MukeshSankhla/Forest-Guard/images/3.png

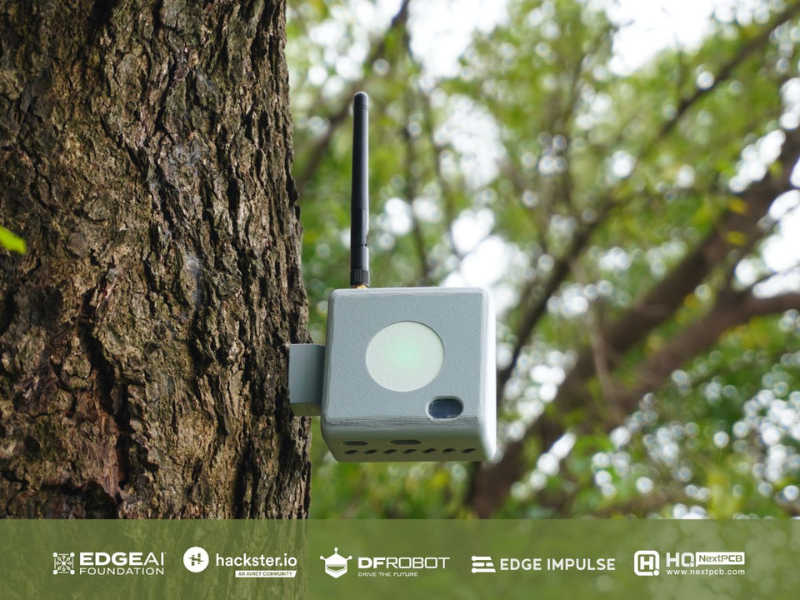
images/3.png
