MukeshSankhla/Forest-Guard/images/S91.JPG

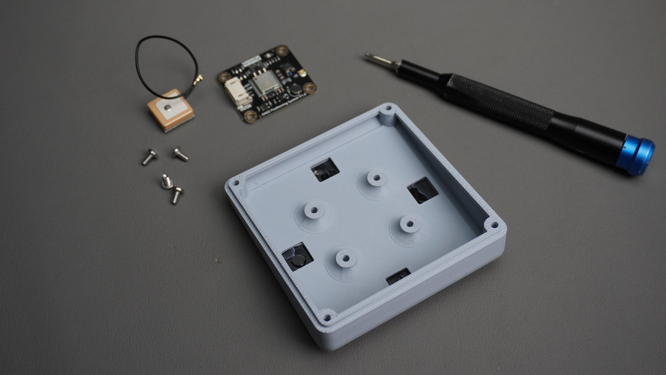
images/S91.JPG
