MukeshSankhla/Forest-Guard/images/ST268.JPG

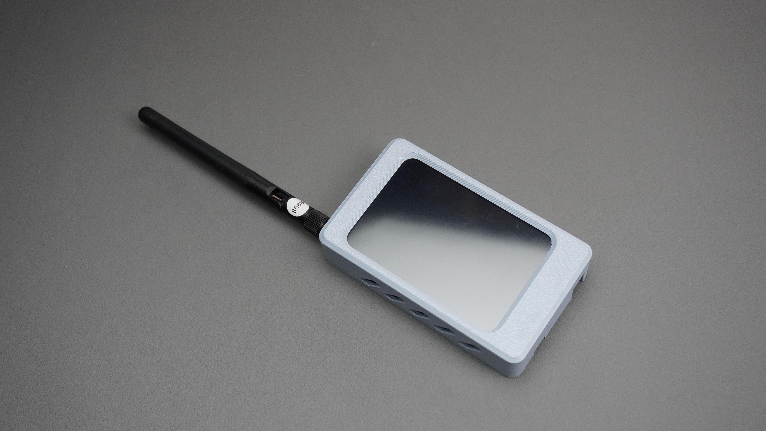
images/ST268.JPG
