MukeshSankhla/Forest-Guard/images/ST277.JPG

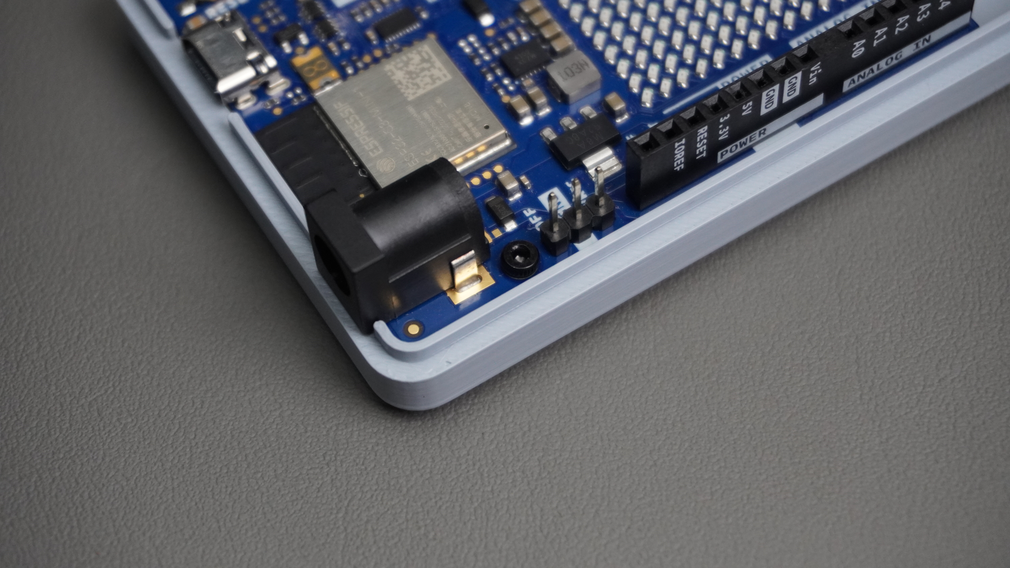
images/ST277.JPG
