MukeshSankhla/Forest-Guard/images/ST312.png

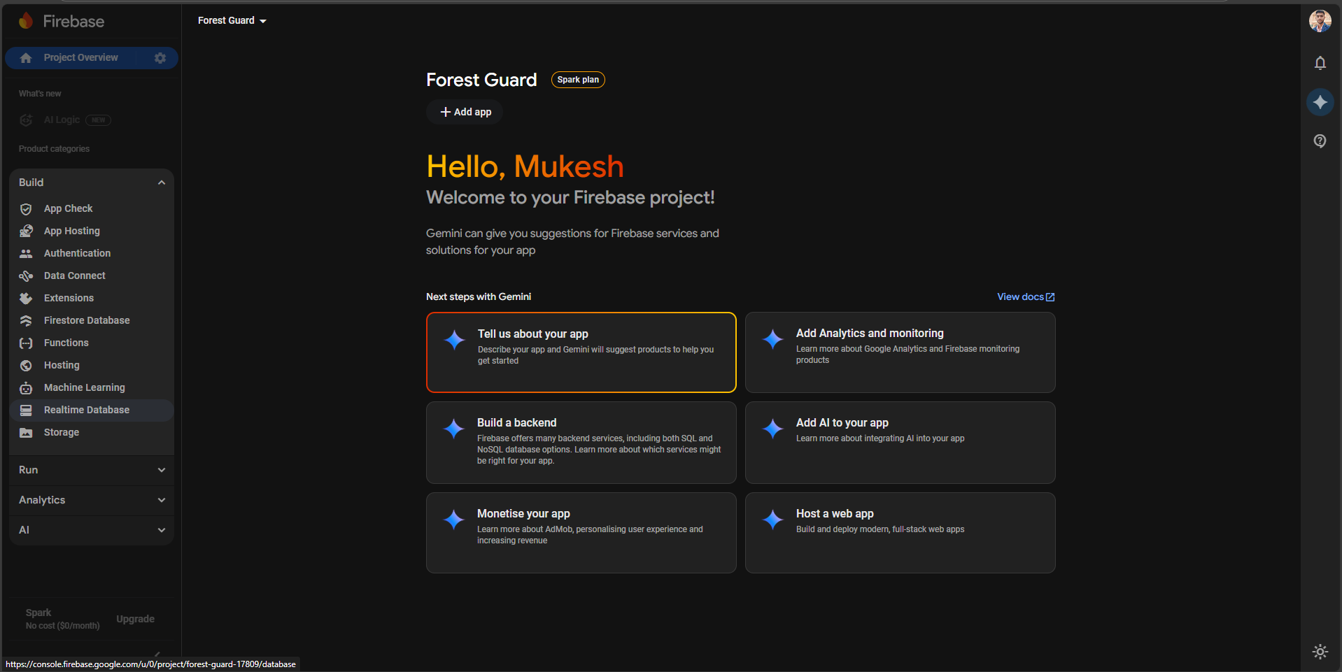
images/ST312.png
