MukeshSankhla/Forest-Guard/images/ST3110.png

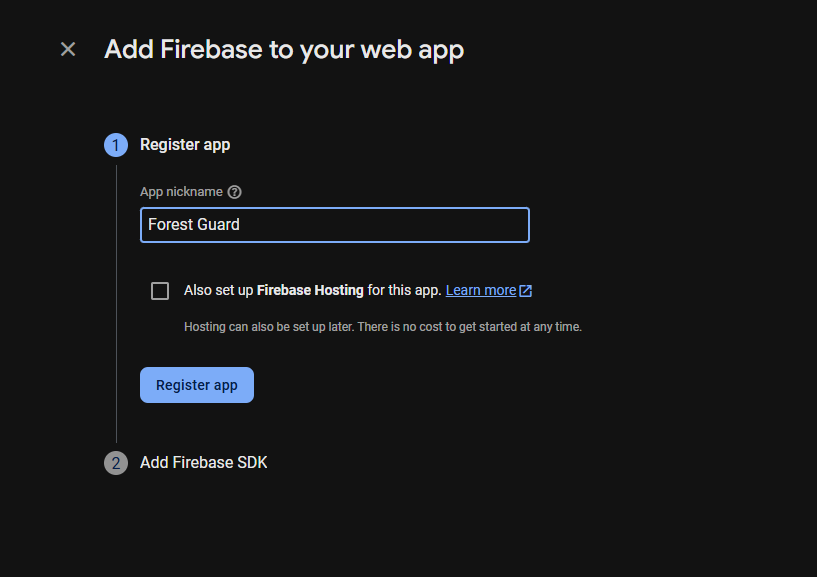
images/ST3110.png
